NomadJoeviolet/ChipTanks/ChipTanksPic/Bo.png

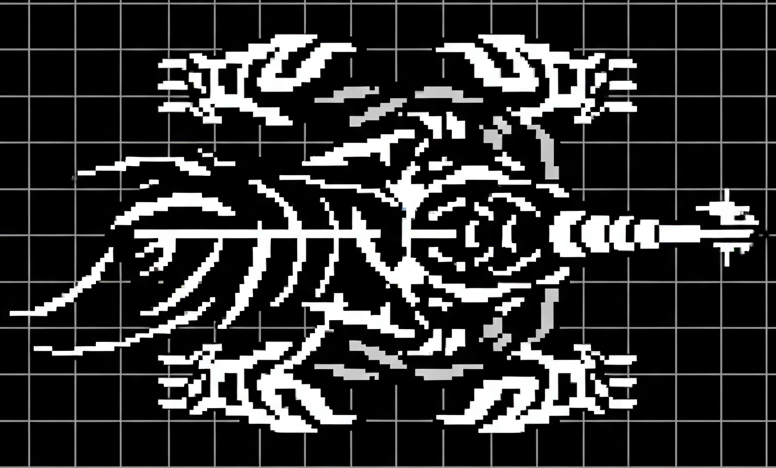
ChipTanksPic/Bo.png
