NomadJoeviolet/ChipTanks/ChipTanksPic/feilian.png

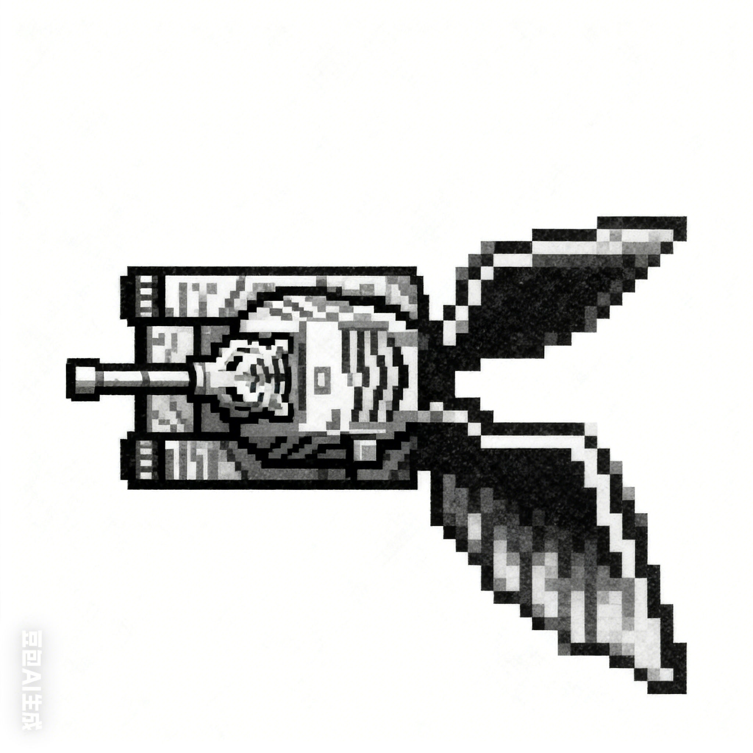
ChipTanksPic/feilian.png
