NomadJoeviolet/ChipTanks/ChipTanksPic/Shengyu.png

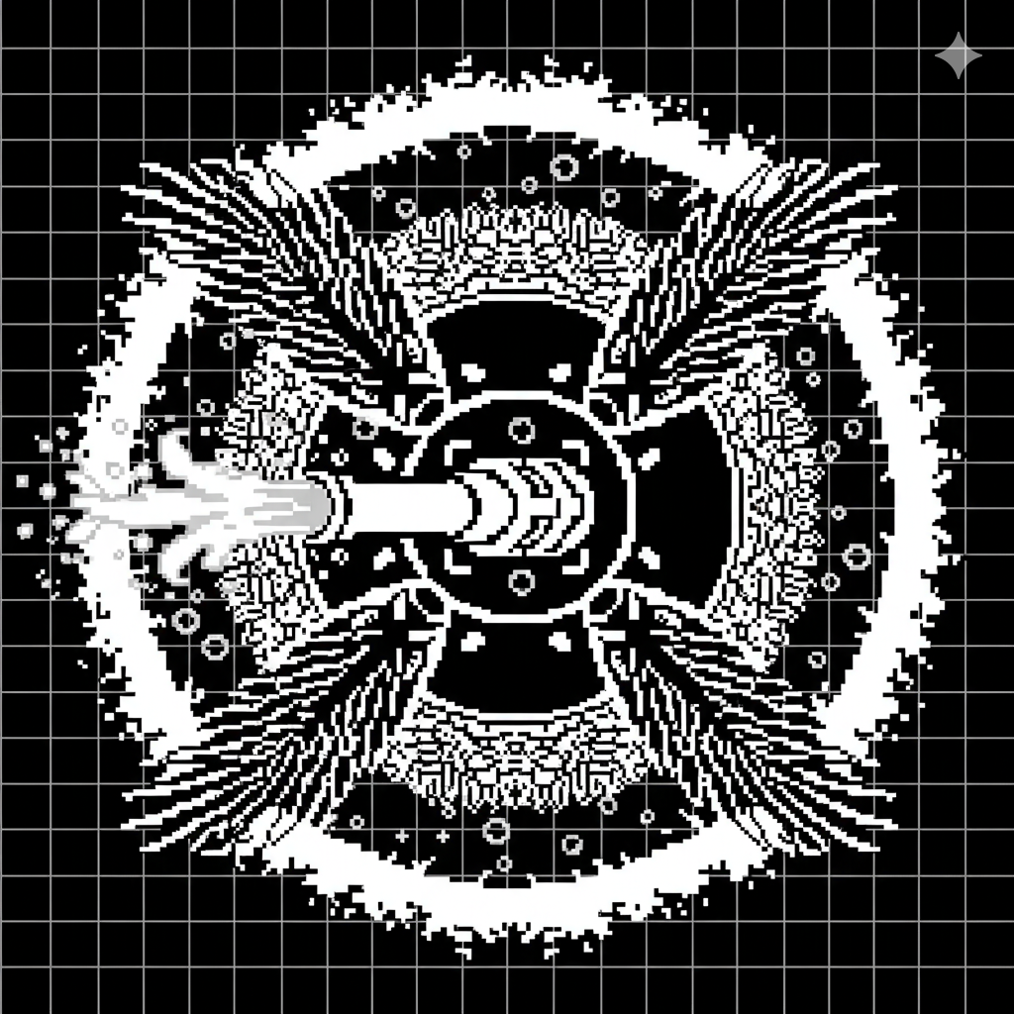
ChipTanksPic/Shengyu.png
