NomadJoeviolet/ChipTanks/App/gameEntityManager.hpp

#ifndef GAMEENTITYMANAGER_HPP
#define GAMEENTITYMANAGER_HPP

#include "math.h"
#include "role.hpp"
#include "leadingRole.hpp"
#include "enemyRole.hpp"
#include "etl/vector.h"

#include "FreeRTOS.h"
#include "task.h"


// 管理游戏中的实体：角色和子弹
// 会被多个模块引用
// 归gameProgressManager管理

class GameEntityManager {
public:
    etl::vector<IRole *, 20>    m_roles;   //角色池，存放所有角色指针
    etl::vector<IBullet *, 100> m_bullets; //子弹池，存放所有子弹指针
    bool                       isGameOver = false;
public:
    GameEntityManager() = default;
    ~GameEntityManager() {
        cleanUpAllRoles(true);
        cleanUpAllBullets(true);
    }
    GameEntityManager(const GameEntityManager &)            = delete;
    GameEntityManager &operator=(const GameEntityManager &) = delete;

public:
    //Add添加
    /********************************************************************/
    bool addRole(IRole *role) {
        if (role == nullptr || m_roles.full()) return false;

        taskENTER_CRITICAL();
        m_roles.push_back(role);
        taskEXIT_CRITICAL();

        return true;
    }

    bool addBullet(IBullet *bullet) {
        if (bullet == nullptr || m_bullets.full()) return false;

        taskENTER_CRITICAL();
        m_bullets.push_back(bullet);
        taskEXIT_CRITICAL();

        return true;
    }
    /********************************************************************/

    //remove删除并销毁
    /********************************************************************/
    bool removeAndDestroyRole(IRole *role) {
        if (role == nullptr) return false;

        taskENTER_CRITICAL();
        auto it = etl::find(m_roles.begin(), m_roles.end(), role);
        if (it != m_roles.end()) {
            m_roles.erase(it);
            delete role;
            taskEXIT_CRITICAL();
            return true;
        }
        taskEXIT_CRITICAL();
        return false;
    }

    bool removeAndDestroyBullet(IBullet *bullet) {
        if (bullet == nullptr) return false;

        taskENTER_CRITICAL();
        auto it = etl::find(m_bullets.begin(), m_bullets.end(), bullet);
        if (it != m_bullets.end()) {
            m_bullets.erase(it);
            delete bullet;
            taskEXIT_CRITICAL();
            return true;
        }
        taskEXIT_CRITICAL();
        return false;
    }
    /********************************************************************/

    //获取player角色指针
    /********************************************************************/
    IRole *getPlayerRole() {
        taskENTER_CRITICAL();
        for (auto role : m_roles) {
            if (role != nullptr && role->getData()->identity == RoleIdentity::Player) {
                taskEXIT_CRITICAL();
                return role;
            }
        }
        taskEXIT_CRITICAL();
        return nullptr;
    }
    /********************************************************************/

    //清除需要回收的角色和子弹
    /********************************************************************/
    void cleanupInvalidRoles() {
        taskENTER_CRITICAL();
        auto it = m_roles.begin();
        while (it != m_roles.end()) {
            IRole *rolePtr = *it;
            if (rolePtr != nullptr && !rolePtr->isActive() ) {
                if(rolePtr->getData()->identity == RoleIdentity::ENEMY) {
                    //获取掉落经验值
                    gainDropExperiencePoints(rolePtr->getData()->deathData.dropExperiencePoints);
                }
                else if(rolePtr->getData()->identity == RoleIdentity::Player) {
                    //可能是召唤物，获取掉落经验值
                    isGameOver = true;
                }
                it = m_roles.erase(it);
                delete rolePtr;
                rolePtr = nullptr;

            } else {
                ++it;
            }
        }
        taskEXIT_CRITICAL();
    }

    void cleanupInvalidBullets() {
        taskENTER_CRITICAL();
        auto it = m_bullets.begin();
        while (it != m_bullets.end()) {
            IBullet *bulletPtr = *it;
            if (bulletPtr != nullptr && !bulletPtr->isActive()) {
                it = m_bullets.erase(it);
                delete bulletPtr;
                bulletPtr = nullptr;
            } else {
                ++it;
            }
        }
        taskEXIT_CRITICAL();
    }
    /********************************************************************/

    //碰撞检测
    /********************************************************************/

    CollisionResult checkRoleRefPositionCollision(IRole *role_A) {
        CollisionResult collisionDetected = {false, CollisionDirection::NONE};

        if (role_A == nullptr) return collisionDetected;
        taskENTER_CRITICAL();
        for (auto role_B : m_roles) {
            if (role_B == nullptr || role_B == role_A) continue;
            // Simple AABB collision detection
            RoleData *dataA = role_A->getData();
            RoleData *dataB = role_B->getData();

            if (dataA->spatialData.refPosX < dataB->spatialData.currentPosX + dataB->spatialData.sizeX
                && dataA->spatialData.refPosX + dataA->spatialData.sizeX > dataB->spatialData.currentPosX
                && dataA->spatialData.refPosY < dataB->spatialData.currentPosY + dataB->spatialData.sizeY
                && dataA->spatialData.refPosY + dataA->spatialData.sizeY > dataB->spatialData.currentPosY) {
                collisionDetected.isCollision = true;

                if (role_A->getData()->identity != role_B->getData()->identity) {
                    role_A->takeDamage(role_B->getData()->attackData.collisionPower); // damage value on collision
                    role_B->takeDamage(role_A->getData()->attackData.collisionPower); // damage value on collision
                }

                // --- 开始：严谨的碰撞方向判断 ---
                // 计算两个角色中心的坐标
                float centerA_X = dataA->spatialData.refPosX + dataA->spatialData.sizeX / 2.0f;
                float centerA_Y = dataA->spatialData.refPosY + dataA->spatialData.sizeY / 2.0f;
                float centerB_X = dataB->spatialData.currentPosX + dataB->spatialData.sizeX / 2.0f;
                float centerB_Y = dataB->spatialData.currentPosY + dataB->spatialData.sizeY / 2.0f;

                // 计算两个中心之间的向量
                float dx = centerA_X - centerB_X;
                float dy = centerA_Y - centerB_Y;

                // 计算两个矩形合并后的总宽度和总高度的一半
                float combinedHalfWidth  = (dataA->spatialData.sizeX + dataB->spatialData.sizeX) / 2.0f;
                float combinedHalfHeight = (dataA->spatialData.sizeY + dataB->spatialData.sizeY) / 2.0f;

                // 计算X和Y轴上的重叠量
                float overlapX = combinedHalfWidth - fabsf(dx);
                float overlapY = combinedHalfHeight - fabsf(dy);

                // 比较重叠量，重叠小的那个轴是碰撞发生的轴
                if (overlapX < overlapY) {
                    // 水平碰撞
                    if (dx > 0) { // A的中心在B的右边
                        collisionDetected.direction = CollisionDirection::RIGHT;
                    } else { // A的中心在B的左边
                        collisionDetected.direction = CollisionDirection::LEFT;
                    }
                } else {
                    // 垂直碰撞
                    if (dy > 0) { // A的中心在B的下边
                        collisionDetected.direction = CollisionDirection::DOWN;
                    } else { // A的中心在B的上边
                        collisionDetected.direction = CollisionDirection::UP;
                    }
                }
                // --- 结束：严谨的碰撞方向判断 ---
                break;
            }
        }
        taskEXIT_CRITICAL();
        return collisionDetected;
    }

    bool checkBulletRefPositionCollision(IBullet *bullet_A) {
        bool collisionDetected = false;
        if (bullet_A == nullptr) return false;
        if (bullet_A->m_data->deathData.isDead) return false;
        if (bullet_A->m_data->isActive == false) return false;

        taskENTER_CRITICAL();
        for (auto role_B : m_roles) {
            if (role_B == nullptr) continue;
            // Simple AABB collision detection
            BulletData *dataA = bullet_A->m_data;
            RoleData   *dataB = role_B->getData();

            if (dataA->fromIdentity == dataB->identity) {
                continue; // Skip collision check if bullet and role have the same identity
            }

            if (dataA->spatialData.refPosX < dataB->spatialData.currentPosX + dataB->spatialData.sizeX - 1
                && dataA->spatialData.refPosX + dataA->spatialData.sizeX - 1 > dataB->spatialData.currentPosX
                && dataA->spatialData.refPosY < dataB->spatialData.currentPosY + dataB->spatialData.sizeY - 1
                && dataA->spatialData.refPosY + dataA->spatialData.sizeY - 1 > dataB->spatialData.currentPosY) {
                collisionDetected = true;
                role_B->takeDamage(dataA->damage); // Apply damage to the role
                //所有角色都要检查碰撞，因为子弹可能穿透多个目标
            }
        }
        taskEXIT_CRITICAL();
        return collisionDetected;
    }
    /********************************************************************/

    //子弹范围伤害检测
    /********************************************************************/

    void checkBulletRangeDamage(IBullet *bullet_A) {
        if (bullet_A == nullptr) return;
        BulletData *dataA = bullet_A->m_data;
        if (dataA->range == 0) return; // No range damage for zero range

        taskENTER_CRITICAL();
        for (auto role_B : m_roles) {
            if (role_B == nullptr) continue;
            // Simple circular range damage detection
            RoleData *dataB = role_B->getData();
            // Skip if same identity
            if (dataA->fromIdentity == dataB->identity) {
                continue;
            }
            // Calculate distance between bullet and role centers
            float centerA_X = dataA->spatialData.currentPosX + dataA->spatialData.sizeX / 2.0f;
            float centerA_Y = dataA->spatialData.currentPosY + dataA->spatialData.sizeY / 2.0f;
            float centerB_X = dataB->spatialData.currentPosX + dataB->spatialData.sizeX / 2.0f;
            float centerB_Y = dataB->spatialData.currentPosY + dataB->spatialData.sizeY / 2.0f;
            float dx        = centerA_X - centerB_X;
            float dy        = centerA_Y - centerB_Y;
            float distance  = sqrtf(dx * dx + dy * dy);
            if (distance <= dataA->range) {
                role_B->takeDamage(dataA->damage); // Apply damage to the role
            }
        }
        taskEXIT_CRITICAL();
    }
    /********************************************************************/

    //更新所有实体位置和状态
    /********************************************************************/
    /**
     * @brief 更新所有角色状态和位置
     */
    void updateAllRolesState() {
        taskENTER_CRITICAL();
        for (auto rolePtr : m_roles) {
            if (rolePtr != nullptr) {
                CollisionResult collisionResult = {false, CollisionDirection::NONE};
                if (rolePtr->getData()->initData.isInited) {
                    //碰撞处理
                    collisionResult = checkRoleRefPositionCollision(rolePtr);
                }
                rolePtr->update(collisionResult);
                
                if(rolePtr->getData()->identity == RoleIdentity::Player) {
                    LeadingRole* playerRole = (LeadingRole*)rolePtr;
                    playerRole->levelUp(); //检查升级
                    playerRole->updateWingmans();
                }
            }
        }
        taskEXIT_CRITICAL();
    }

    /**
     * @brief 更新所有子弹状态和位置
     */
    void updateAllBulletsState() {
        taskENTER_CRITICAL();
        for (auto bulletPtr : m_bullets) {
            if (bulletPtr != nullptr) {
                CollisionResult collisionResult = {false, CollisionDirection::NONE};
                //碰撞处理
                bool isCollision = checkBulletRefPositionCollision(bulletPtr);
                if (isCollision) {
                    collisionResult.isCollision = true;
                    checkBulletRangeDamage(bulletPtr);
                }
                bulletPtr->update(collisionResult);
            }
        }
        taskEXIT_CRITICAL();
    }
    /********************************************************************/

    // 更新所有角色的AI行动决策
    /********************************************************************/
    void updateAllRolesActions() {
        taskENTER_CRITICAL();
        for (auto rolePtr : m_roles) {
            if (rolePtr != nullptr && rolePtr->getData()->initData.isInited) {
                rolePtr->think();
                rolePtr->doAction();
            }
        }
        taskEXIT_CRITICAL();
    }

    void updateAllBulletsActions() {
        taskENTER_CRITICAL();
        for (auto bulletPtr : m_bullets) {
            if (bulletPtr != nullptr) {
                bulletPtr->doAction();
            }
        }
        taskEXIT_CRITICAL();
    }
    /********************************************************************/

    // 绘制所有实体
    /********************************************************************/
    void drawAllRoles() {
        taskENTER_CRITICAL();
        for (auto rolePtr : m_roles) {
            if (rolePtr != nullptr && rolePtr->getData() != nullptr && rolePtr->getData()->img != nullptr) {
                rolePtr->drawRole();
            }
        }
        taskEXIT_CRITICAL();
    }

    void drawAllBullets() {
        taskENTER_CRITICAL();
        for (auto bulletPtr : m_bullets) {
            if (bulletPtr != nullptr && bulletPtr->m_data != nullptr && bulletPtr->m_data->img != nullptr) {
                bulletPtr->drawBullet();
            }
        }
        taskEXIT_CRITICAL();
    }

    /********************************************************************/

    //清除所有实体，资源回收
    void clearAllEntities(bool deleteObjects = true) {
        cleanUpAllRoles(deleteObjects);
        cleanUpAllBullets(deleteObjects);
    }

private:
    //清除所有角色和子弹，资源回收
    /********************************************************************/

    void cleanUpAllRoles(bool deleteObjects = true) {
        if (!deleteObjects) return;
        for (auto rolePtr : m_roles) {
            if (rolePtr != nullptr) delete rolePtr;
        }
        m_roles.clear();
    }
    void cleanUpAllBullets(bool deleteObjects = true) {
        if (!deleteObjects) return;
        for (auto bulletPtr : m_bullets) {
            if (bulletPtr != nullptr) delete bulletPtr;
        }
        m_bullets.clear();
    }
    /********************************************************************/

    //玩家角色获取经验值
    /********************************************************************/
    void gainDropExperiencePoints(uint16_t points) {
        LeadingRole* playerRole = (LeadingRole*)getPlayerRole();
        if (playerRole != nullptr && playerRole->getData()->level < 15) {
            playerRole->experiencePoints += points;
        }
    }
    /********************************************************************/
};

#endif // GAMEENTITYMANAGER_HPP
