NomadJoeviolet/ChipTanks/App/gamePerkCardManager.hpp

#ifndef GAMEPERKCARDMANAGER_HPP
#define GAMEPERKCARDMANAGER_HPP
#include "etl/vector.h"

#include "oled.h"
#include "prekCard.hpp"
#include "gameEntityManager.hpp"
#include "leadingRole.hpp"

// 管理游戏中的Perk卡片系统
// 引用GameEntityManager实例
// 归gameProgressManager管理

extern GameEntityManager g_entityManager;

class GamePerkCardManager {
public:
    GamePerkCardManager()  = default;
    ~GamePerkCardManager() = default;

    GamePerkCardManager(const GamePerkCardManager &)            = delete;
    GamePerkCardManager &operator=(const GamePerkCardManager &) = delete;

private:
    static const uint8_t MAX_CARD_COUNT       = 28; // 总卡片数（2*10 +1*8=28）
    static const uint8_t SELECTION_SLOT_COUNT = 3;  // 选卡槽数量（3张）

    etl::vector<PerkCard, MAX_CARD_COUNT>       m_cardWarehouse;  // 卡片仓库（存所有卡片）
    etl::vector<PerkCard, SELECTION_SLOT_COUNT> m_selectionSlots; // 选卡槽（临时存3张待选）

public:
    bool    isInited           = false; // 是否已初始化
    bool    m_isSelecting      = false; // 选卡状态（标记是否处于"选卡中"，避免重复触发）
    uint8_t m_selectedIndex    = 0;     // 选中卡片索引（选卡槽内索引）
    uint8_t m_selectedSize     = 0;     // 选中卡片数量（选卡槽内数量）
    uint8_t m_pendingSelections = 0;    // 待处理的选卡次数（解决多事件同时触发时跳过问题）
    uint16_t m_selectionCooldown = 0;   // 选卡冷却计时器（避免连续选卡）

public:
    // 初始化卡片仓库
    void initWarehouse() {
        m_cardWarehouse.clear();
        m_selectionSlots.clear();
        m_isSelecting       = false;
        m_pendingSelections = 0;
        m_selectionCooldown = 0;
        isInited            = true;

        // 遍历配置表，按数量创建卡片并加入仓库
        for (const auto &config : PERK_CARD_CONFIGS) {
            for (uint8_t i = 0; i < config.count; ++i) {
                PerkCard newCard(config.type, config.name, config.param);
                m_cardWarehouse.push_back(newCard);
            }
        }
    }

    bool triggerPerkSelection() {
        if( g_entityManager.isGameOver || !isInited || g_entityManager.getPlayerRole()->getData()->deathData.isDead ) {
            return false; // 游戏结束状态拒绝触发
        }

        if (m_cardWarehouse.empty()) {
            return false; // 无卡片可选，拒绝触发
        }

        // 如果当前已在选卡中，累加待选次数，等当前选卡完成后再触发
        if (m_isSelecting) {
            m_pendingSelections++;
            return true; // 已记录待选，返回成功
        }

        m_selectionSlots.clear();

        // 可用卡片不足3张时，取全部（避免选卡槽为空）
        uint8_t selectCount = etl::min(SELECTION_SLOT_COUNT, (uint8_t)m_cardWarehouse.size());
        if (selectCount == 0) {
            return false; // 无可用卡片
        }
        m_selectedSize = selectCount;
        // 随机抽取selectCount张卡片，放入选卡槽（从仓库移除，避免重复抽）
        for (uint8_t i = 0; i < selectCount; ++i) {
            // 嵌入式随机算法：用系统滴答定时器做模运算（无需rand()）
            uint8_t randIdx      = rand() % m_cardWarehouse.size();
            uint8_t warehouseIdx = randIdx;

            // 从仓库移动到选卡槽（避免拷贝，提升效率）
            m_selectionSlots.push_back(m_cardWarehouse[warehouseIdx]);
            m_cardWarehouse.erase(m_cardWarehouse.begin() + warehouseIdx);
        }
        // 标记为选卡中，UI提示
        m_isSelecting = true;

        return true;
    }

    bool selectCard(uint8_t slotIndex) {
        // 前置校验：1. 在选卡中；2. 槽索引有效
        if (!m_isSelecting || slotIndex >= m_selectionSlots.size()) {
            return false;
        }

        // 处理选中卡片（slotIndex）
        PerkCard     selectedCard = m_selectionSlots[slotIndex];
        LeadingRole *player       = (LeadingRole *)g_entityManager.getPlayerRole();

        if (player == nullptr) {
            return false; // 未找到玩家角色，无法应用卡片效果
        }

        // 应用卡片效果
        switch (selectedCard.type) {
        case PerkCardType::HEAL_SPEED_UP:
            player->getData()->healthData.healSpeed += selectedCard.param;
            break;
        case PerkCardType::HEAL_AMOUNT_UP:
            player->getData()->healthData.healValue += selectedCard.param;
            break;
        case PerkCardType::HEALTH_UP:
            player->getData()->healthData.maxHealth += selectedCard.param;
            player->getData()->healthData.currentHealth = player->getData()->healthData.maxHealth;
            break;
        case PerkCardType::ATTACK_UP:
            player->getData()->attackData.attackPower += selectedCard.param;
            break;
        case PerkCardType::ATTACK_SPEED_UP:
            player->getData()->attackData.shootCooldownSpeed += selectedCard.param;
            break;
        case PerkCardType::HEAT_CAPACITY_UP:
            player->getData()->heatData.maxHeat += selectedCard.param;
            break;
        case PerkCardType::HEAT_COOL_DOWN_UP:
            player->getData()->heatData.heatCoolDownRate += selectedCard.param;
            break;
        case PerkCardType::UNLOCK_FIREBALL:
            player->bulletTypeOwned.fireBallBulletOwed = 1;
            break;
        case PerkCardType::UNLOCK_LIGHTNING:
            player->bulletTypeOwned.lightningLineBulletOwed = 1;
            break;
        case PerkCardType::FIREBALL_RANGE_UP:
            player->getData()->attackData.bulletRange += selectedCard.param;
            break;
        case PerkCardType::LIGHTNING_MULTIPLIER_UP:
            player->getData()->attackData.bulletDamageMultiplier += (static_cast<float>(selectedCard.param) / 10.0f);
            break;
        case PerkCardType::MOVE_SPEED_UP:
            player->getData()->spatialData.moveSpeed += selectedCard.param;
            break;
        case PerkCardType::HEALTH_UP_PRO:
            player->getData()->healthData.maxHealth += selectedCard.param;
            player->getData()->healthData.currentHealth = player->getData()->healthData.maxHealth;
            break;
        case PerkCardType::HEAL_SPEED_UP_PRO:
            player->getData()->healthData.healSpeed += selectedCard.param;
            break;
        case PerkCardType::HEAL_AMOUNT_UP_PRO:
            player->getData()->healthData.healValue += selectedCard.param;
            break;
        case PerkCardType::UNLOCK_PHOENIX:
            player->phoenixWingmanOwned = true;
            break;
        case PerkCardType::UNLOCK_KUINIU:
            player->kuiniuWingmanOwned = true;
            break;
        case PerkCardType::MAGIC_TIM:
            player->magicTimOwned = true;
            break;
        default:
            break;
        }

        // 移除选中卡片，清理未选中卡片，重置选卡状态
        m_selectionSlots.erase(m_selectionSlots.begin() + slotIndex);
        returnUnselectedCards();

        m_isSelecting = false;
        m_selectionCooldown = 200; // 设置200ms冷却，避免连续选卡

        // 检查是否有待处理的选卡次数，如果有则立即触发下一次选卡
        if (m_pendingSelections > 0) {
            m_pendingSelections--;
            triggerPerkSelection(); // 递归触发下一次选卡
        }

        return true;
    }

    // 更新选卡冷却计时器（需要在游戏主循环中调用）
    void updateCooldown(uint16_t deltaTime) {
        if (m_selectionCooldown > 0) {
            if (m_selectionCooldown > deltaTime) {
                m_selectionCooldown -= deltaTime;
            } else {
                m_selectionCooldown = 0;
            }
        }
    }

    // 检查是否在冷却中
    bool isInCooldown() const {
        return m_selectionCooldown > 0;
    }

    // 辅助接口：未选中的卡片回库
    void returnUnselectedCards() {
        for (uint8_t i = 0; i < m_selectionSlots.size(); ++i) {
            // 跳过选中的卡片（slotIndex已处理）
            m_cardWarehouse.push_back(m_selectionSlots[i]);
        }
        m_selectionSlots.clear();
    }

    void drawSelectionUI() {
        if (!m_isSelecting) {
            return; // 非选卡状态，无需绘制
        }
        
        // ===== 科幻风格四角装饰 =====
        // 左上角 - 科幻HUD边角
        OLED_DrawLine(0, 0, 20, 0, OLED_COLOR_NORMAL);
        OLED_DrawLine(0, 0, 0, 15, OLED_COLOR_NORMAL);
        OLED_DrawLine(20, 0, 15, 5, OLED_COLOR_NORMAL);
        OLED_DrawLine(0, 15, 5, 10, OLED_COLOR_NORMAL);
        OLED_DrawFilledRectangle(2, 2, 3, 3, OLED_COLOR_NORMAL);
        
        // 右上角 - 科幻HUD边角
        OLED_DrawLine(127, 0, 107, 0, OLED_COLOR_NORMAL);
        OLED_DrawLine(127, 0, 127, 15, OLED_COLOR_NORMAL);
        OLED_DrawLine(107, 0, 112, 5, OLED_COLOR_NORMAL);
        OLED_DrawLine(127, 15, 122, 10, OLED_COLOR_NORMAL);
        OLED_DrawFilledRectangle(122, 2, 3, 3, OLED_COLOR_NORMAL);
        
        // 左下角 - 科幻HUD边角
        OLED_DrawLine(0, 63, 20, 63, OLED_COLOR_NORMAL);
        OLED_DrawLine(0, 63, 0, 48, OLED_COLOR_NORMAL);
        OLED_DrawLine(20, 63, 15, 58, OLED_COLOR_NORMAL);
        OLED_DrawLine(0, 48, 5, 53, OLED_COLOR_NORMAL);
        OLED_DrawFilledRectangle(2, 58, 3, 3, OLED_COLOR_NORMAL);
        
        // 右下角 - 科幻HUD边角
        OLED_DrawLine(127, 63, 107, 63, OLED_COLOR_NORMAL);
        OLED_DrawLine(127, 63, 127, 48, OLED_COLOR_NORMAL);
        OLED_DrawLine(107, 63, 112, 58, OLED_COLOR_NORMAL);
        OLED_DrawLine(127, 48, 122, 53, OLED_COLOR_NORMAL);
        OLED_DrawFilledRectangle(122, 58, 3, 3, OLED_COLOR_NORMAL);
        
        // ===== 顶部标题区域 =====
        OLED_DrawLine(25, 3, 102, 3, OLED_COLOR_NORMAL);
        OLED_PrintString(32, 5, "SELECT PERK", &font8x6, OLED_COLOR_NORMAL);
        OLED_DrawLine(25, 14, 102, 14, OLED_COLOR_NORMAL);
        
        // 标题两侧装饰三角
        OLED_DrawTriangle(26, 8, 30, 5, 30, 11, OLED_COLOR_NORMAL);
        OLED_DrawTriangle(101, 8, 97, 5, 97, 11, OLED_COLOR_NORMAL);
        
        // ===== 卡片选项区域 =====
        uint8_t startY = 18;
        uint8_t cardHeight = 14;
        
        for (uint8_t i = 0; i < m_selectionSlots.size(); ++i) {
            uint8_t cardY = startY + (i * cardHeight);
            
            // 选中状态 - 高亮边框
            if (i == m_selectedIndex) {
                // 选中卡片的科幻边框
                OLED_DrawRectangle(8, cardY, 111, cardHeight - 1, OLED_COLOR_NORMAL);
                // 左侧选中指示器 - 箭头
                OLED_DrawFilledTriangle(3, cardY + 2, 3, cardY + cardHeight - 3, 7, cardY + (cardHeight / 2), OLED_COLOR_NORMAL);
                // 右侧装饰
                OLED_DrawFilledTriangle(124, cardY + 2, 124, cardY + cardHeight - 3, 120, cardY + (cardHeight / 2), OLED_COLOR_NORMAL);
            } else {
                // 非选中卡片 - 简单边线
                OLED_DrawLine(12, cardY + cardHeight - 2, 115, cardY + cardHeight - 2, OLED_COLOR_NORMAL);
            }
            
            // 卡片名称
            OLED_PrintString(15, cardY + 3, m_selectionSlots[i].name, &font8x6, OLED_COLOR_NORMAL);
        }
        
        // ===== 底部操作提示 =====
        OLED_DrawLine(25, 60, 102, 60, OLED_COLOR_NORMAL);
        
        // 扫描线动画效果（闪烁）
        static uint8_t scanLinePos = 0;
        scanLinePos = (scanLinePos + 1) % 20;
        if (scanLinePos < 10) {
            OLED_DrawLine(8 + scanLinePos * 5, 17, 8 + scanLinePos * 5 + 3, 17, OLED_COLOR_NORMAL);
        }
    }
};

#endif // GAMEPERKCARDMANAGER_HPP
